BAmercury/PotterMagicLantern/MagicLantern/Colors.h

/*
 * Copyright (c) 2017 Evan Kale
 * Email: EvanKale91@gmail.com
 * Web: www.youtube.com/EvanKale
 * Social: @EvanKale91
 *
 * This file is part of ArduinoGlowingLEDs.
 *
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
 * You should have received a copy of the GNU General Public License
 * along with this program.  If not, see <http://www.gnu.org/licenses/>.
 */

const PROGMEM  uint8_t colors[]  = {
  0x12, 0x61, 0x6b,
  0xf, 0x67, 0x63,
  0x10, 0x66, 0x5a,
  0xf, 0x69, 0x58,
  0xf, 0x69, 0x58,
  0xe, 0x69, 0x4d,
  0xe, 0x66, 0x50,
  0xe, 0x66, 0x52,
  0xd, 0x6a, 0x4d,
  0xd, 0x68, 0x53,
  0xd, 0x65, 0x55,
  0xe, 0x64, 0x59,
  0xd, 0x69, 0x4d,
  0xd, 0x67, 0x4b,
  0xd, 0x67, 0x4b,
  0xd, 0x68, 0x53,
  0xd, 0x67, 0x4a,
  0xf, 0x64, 0x51,
  0xd, 0x67, 0x57,
  0x11, 0x61, 0x67,
  0x10, 0x64, 0x64,
  0xf, 0x67, 0x63,
  0x10, 0x63, 0x64,
  0xe, 0x69, 0x5e,
  0xe, 0x69, 0x57,
  0xf, 0x67, 0x5e,
  0xf, 0x65, 0x5d,
  0xe, 0x68, 0x56,
  0xd, 0x65, 0x49,
  0xc, 0x67, 0x45,
  0xc, 0x68, 0x47,
  0xc, 0x68, 0x47,
  0x11, 0x60, 0x5d,
  0x12, 0x5f, 0x61,
  0x10, 0x60, 0x67,
  0xe, 0x67, 0x5c,
  0xf, 0x67, 0x4b,
  0x10, 0x63, 0x65,
  0x14, 0x5b, 0x79,
  0x16, 0x57, 0x7d,
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
};
